dicarlolab/Fiberscope/Software/mex_code/ALP/ALP-4.2/Samples/sequences/SinglePhotographs/valley_LANDSCAPE-FORMAT.jpg

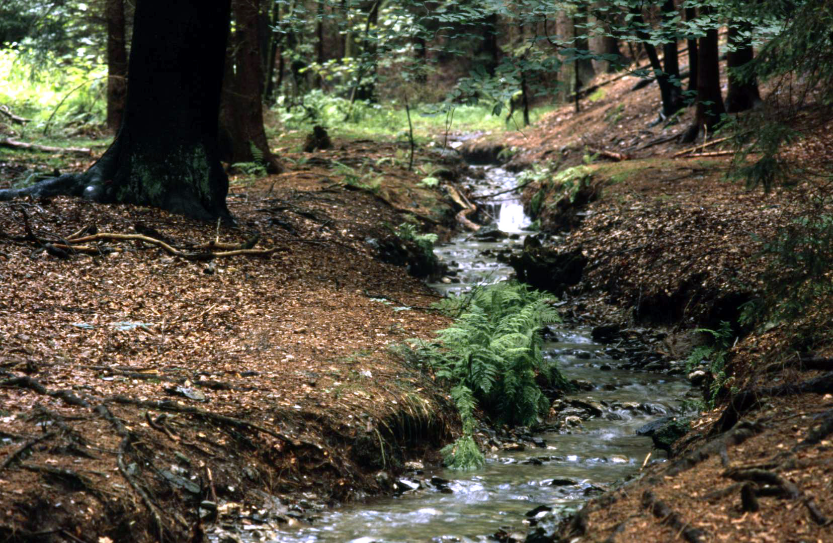
Software/mex_code/ALP/ALP-4.2/Samples/sequences/SinglePhotographs/valley_LANDSCAPE-FORMAT.jpg
