dicarlolab/Fiberscope/Software/mex_code/ALP/ALP-4.2/Samples/sequences/SinglePhotographs/sun-set_PORTRAIT-FORMAT.jpg

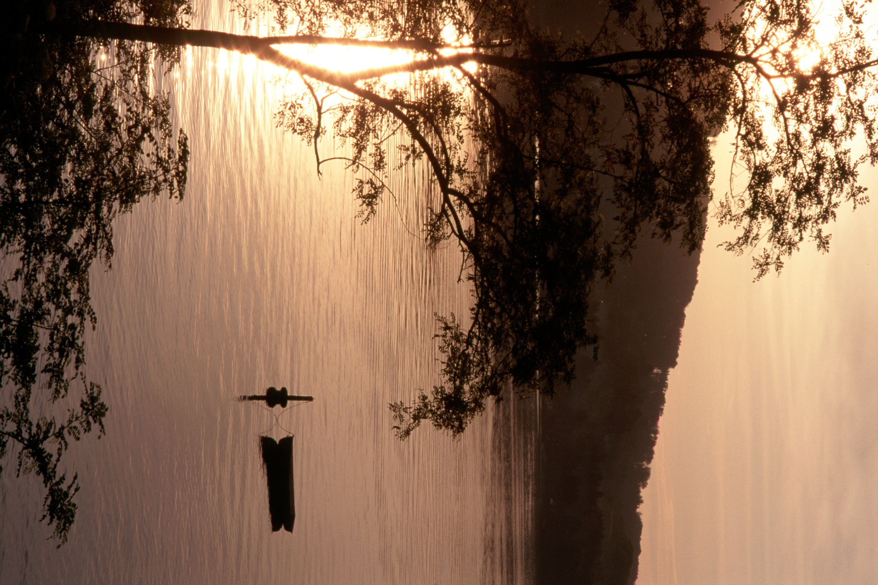
Software/mex_code/ALP/ALP-4.2/Samples/sequences/SinglePhotographs/sun-set_PORTRAIT-FORMAT.jpg
