dicarlolab/Fiberscope/Software/mex_code/ALP/ALP-4.2 v12/Samples/LabVIEW ALP-4.2 high-speed/ALP42_XGA.png

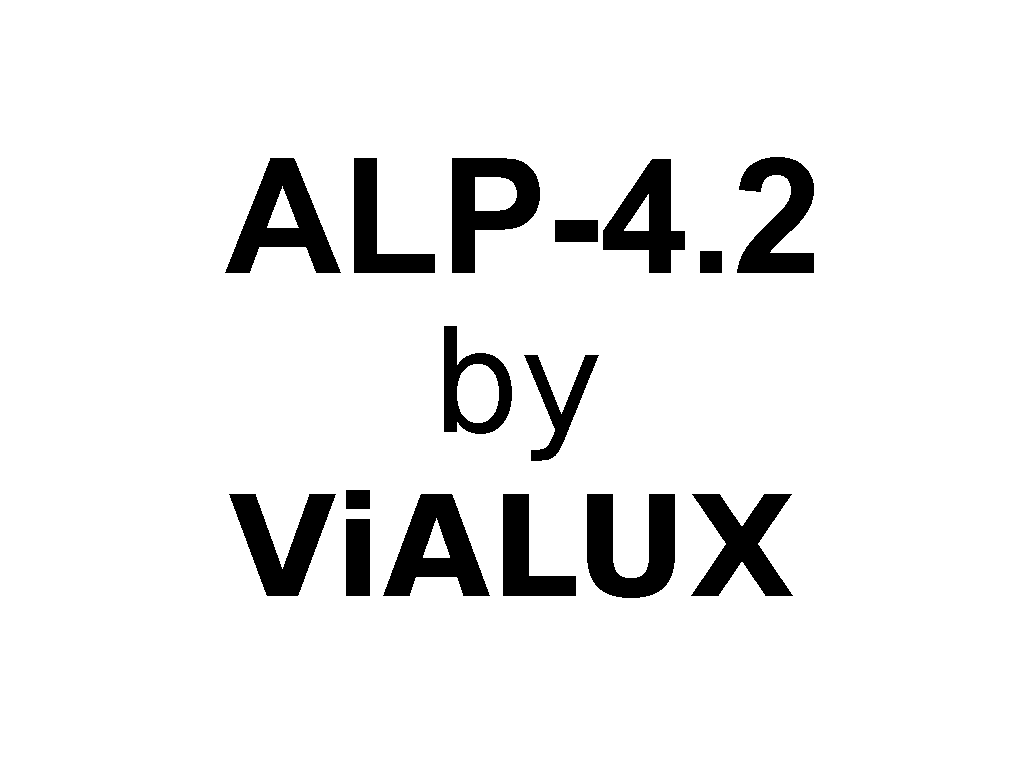
Software/mex_code/ALP/ALP-4.2 v12/Samples/LabVIEW ALP-4.2 high-speed/ALP42_XGA.png
