dicarlolab/Fiberscope/Software/mex_code/ALP/ALP-4.2/Samples/sequences/SequenceTextAndCircle-XGA/ProjectionSequence_Count1024x768_03.png

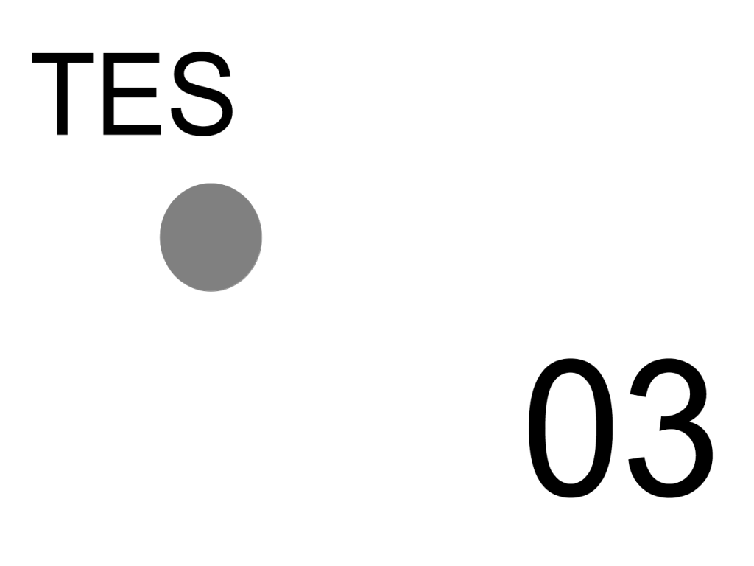
Software/mex_code/ALP/ALP-4.2/Samples/sequences/SequenceTextAndCircle-XGA/ProjectionSequence_Count1024x768_03.png
