dicarlolab/Fiberscope/MechanicalDesign/CP02-Solidworks.sldprt

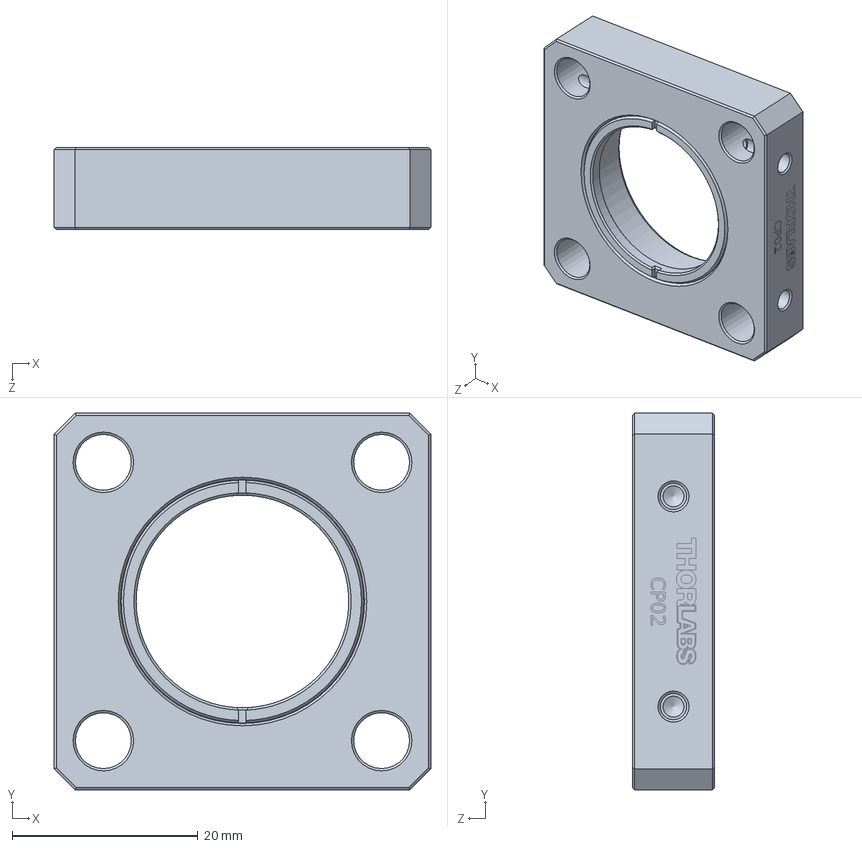
[picture p28: CAD file, 2017-12-06]
MechanicalDesign/CP02-Solidworks.sldprt
40.6 x 40.6 x 8.89 mm
