dicarlolab/Fiberscope/MechanicalDesign/Optic Fiber 105-125um .66NA fiber Neuronexus.SLDPRT

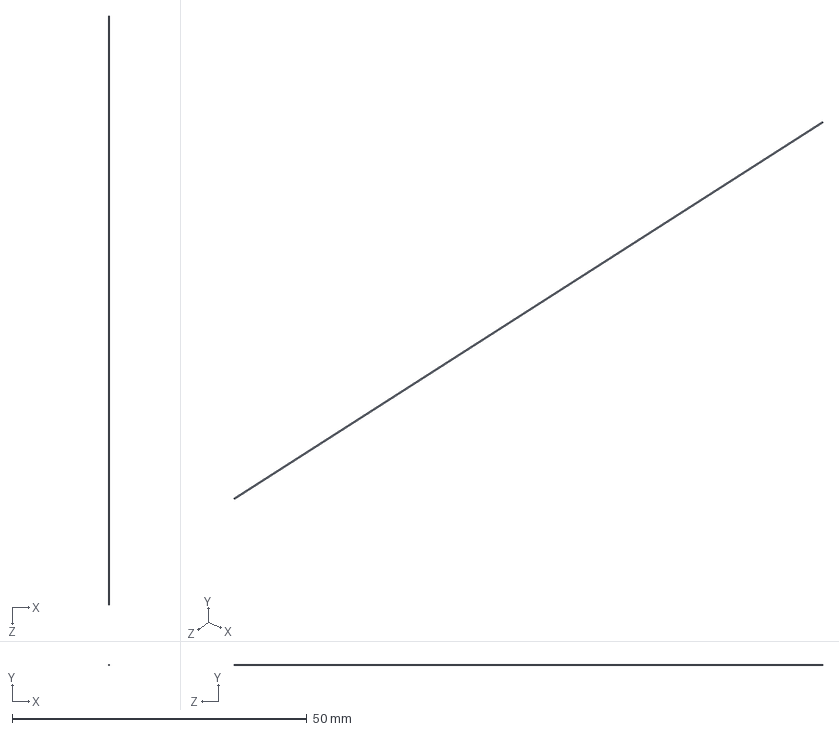
[picture p29: CAD file, 2017-12-06]
MechanicalDesign/Optic Fiber 105-125um .66NA fiber Neuronexus.SLDPRT
0.125 x 0.125 x 100.0 mm
