dicarlolab/Fiberscope/MechanicalDesign/AC127-019-A-ML-Solidworks.sldprt

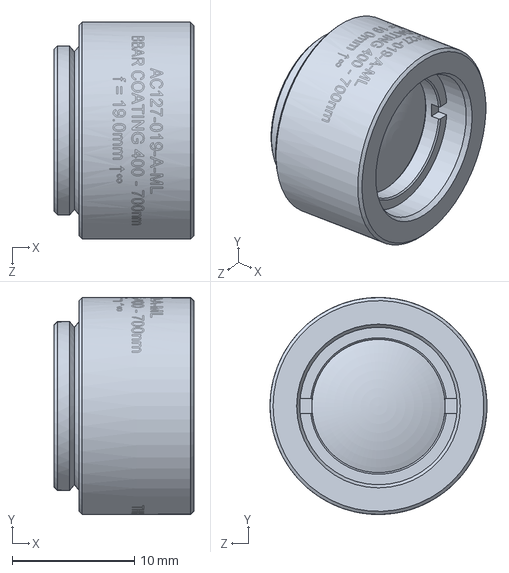
[picture p30: CAD file, 2017-12-06]
MechanicalDesign/AC127-019-A-ML-Solidworks.sldprt
11.4 x 17.8 x 17.8 mm
