dicarlolab/Fiberscope/MechanicalDesign/KM100-E02-Solidworks.sldprt

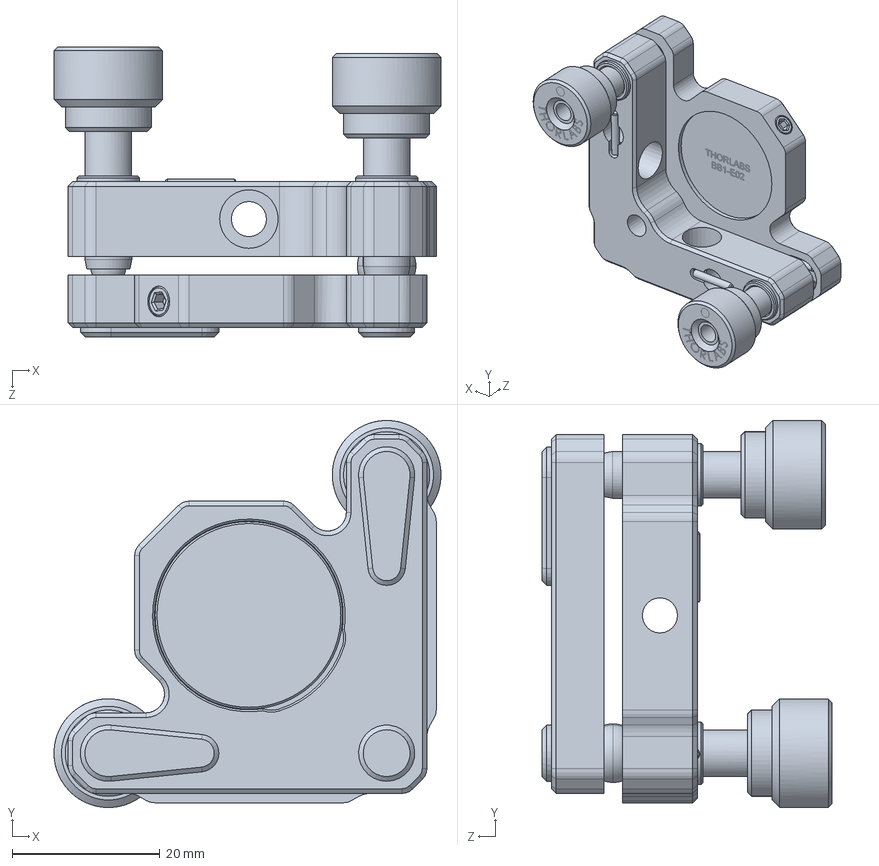
[picture p31: CAD file, 2017-12-06]
MechanicalDesign/KM100-E02-Solidworks.sldprt
52.4 x 52.5 x 39.3 mm
