dicarlolab/Fiberscope/MechanicalDesign/SM05T1-Solidworks.sldprt

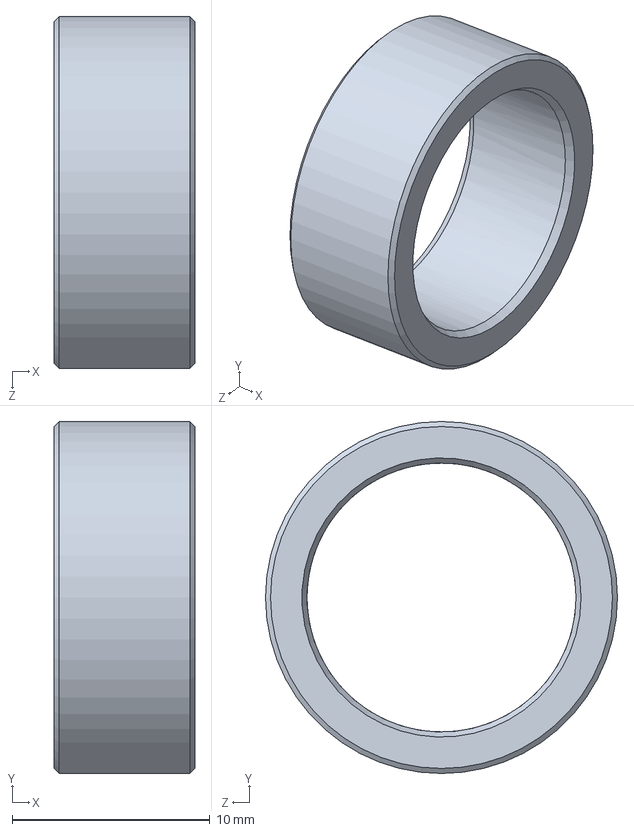
[picture p32: CAD file, 2017-12-06]
MechanicalDesign/SM05T1-Solidworks.sldprt
7.11 x 17.8 x 17.8 mm
