dicarlolab/Fiberscope/MechanicalDesign/SM1L05-Solidworks.sldprt

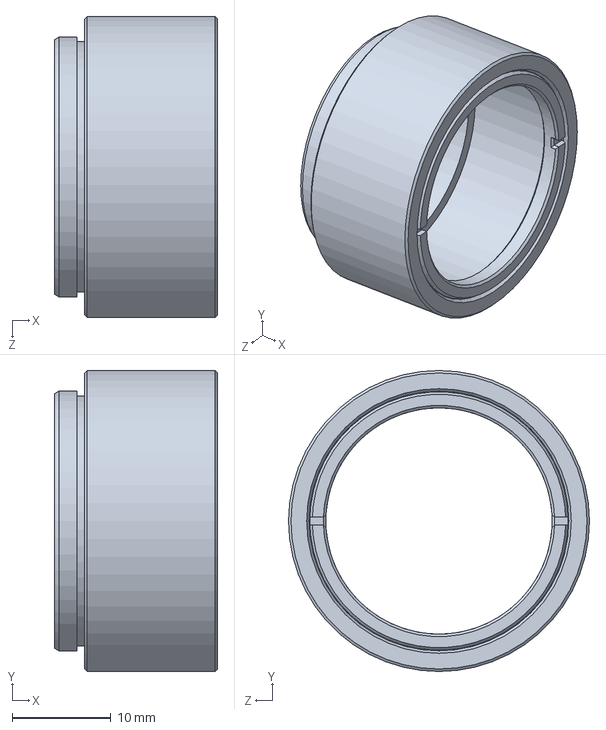
[picture p33: CAD file, 2017-12-06]
MechanicalDesign/SM1L05-Solidworks.sldprt
16.5 x 30.5 x 30.5 mm
