dicarlolab/Fiberscope/MechanicalDesign/SM1A1-Solidworks.sldprt

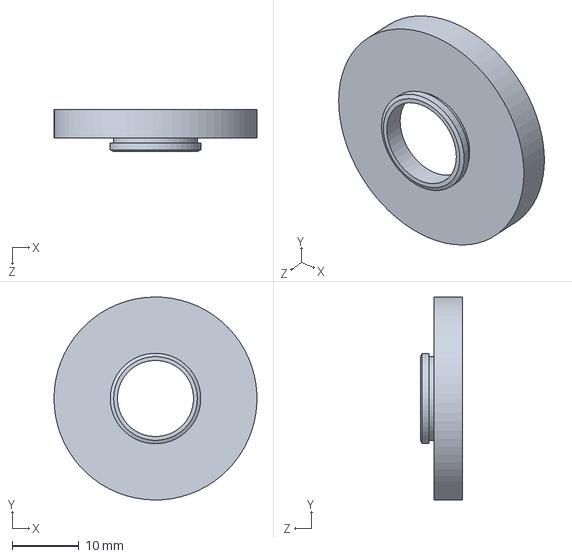
[picture p34: CAD file, 2017-12-06]
MechanicalDesign/SM1A1-Solidworks.sldprt
30.5 x 30.5 x 6.35 mm
