dicarlolab/Fiberscope/MechanicalDesign/Middle_plate_V8Bottom.SLDPRT

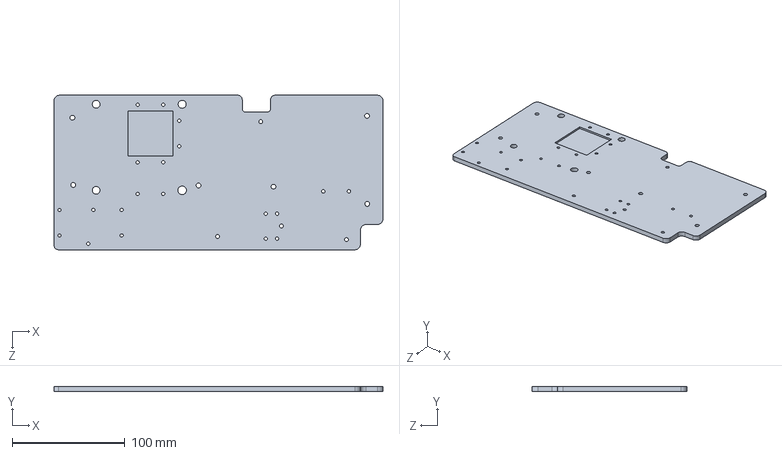
[picture p35: CAD file, 2017-12-06]
MechanicalDesign/Middle_plate_V8Bottom.SLDPRT
291.4 x 4.80 x 137.0 mm
