dicarlolab/Fiberscope/MechanicalDesign/SP05-Solidworks.SLDPRT

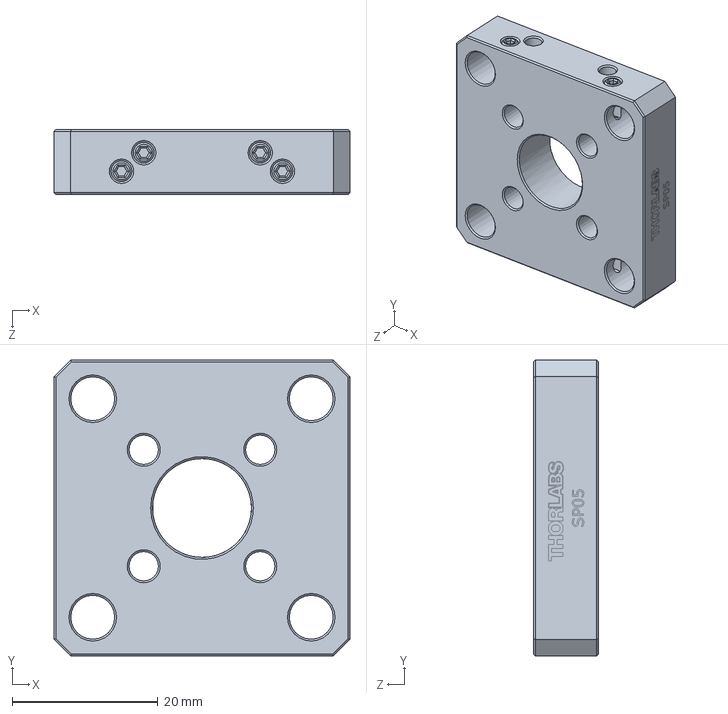
[picture p36: CAD file, 2017-12-06]
MechanicalDesign/SP05-Solidworks.SLDPRT
40.6 x 40.6 x 8.89 mm
