dicarlolab/Fiberscope/MechanicalDesign/CXY1 - 30 mm Cage System, XY Translating Lens Mount for Ø1 Optics .sldprt

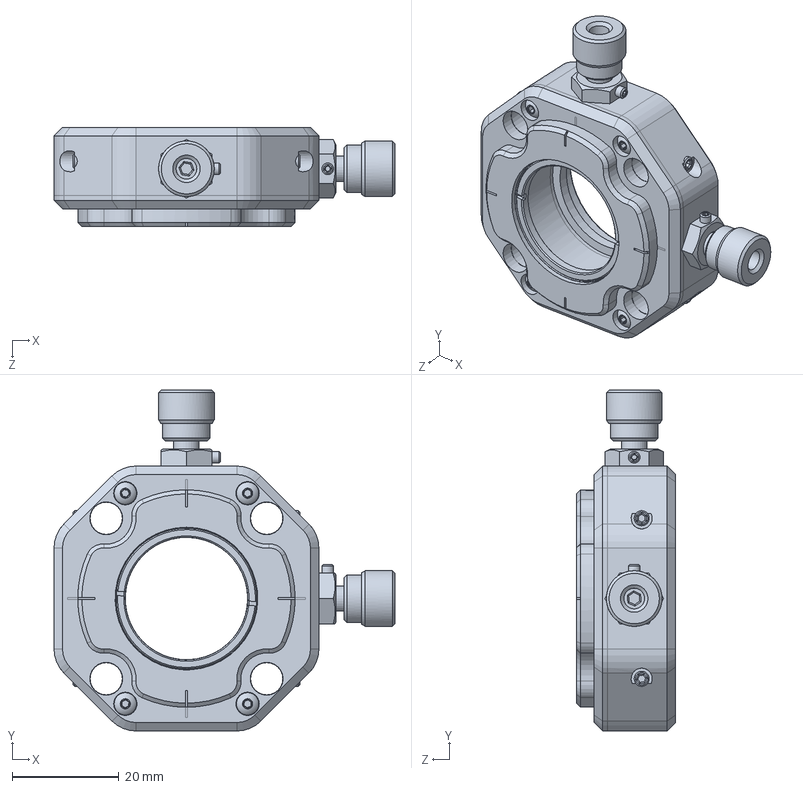
[picture p37: CAD file, 2017-12-06]
MechanicalDesign/CXY1 - 30 mm Cage System, XY Translating Lens Mount for Ø1 Optics .sldprt
63.8 x 63.7 x 18.6 mm
