dicarlolab/Fiberscope/MechanicalDesign/AC254-125-A-ML-Solidworks.sldprt

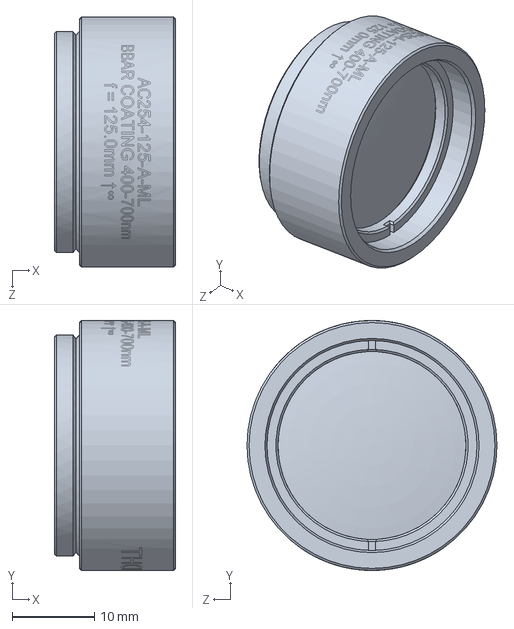
[picture p38: CAD file, 2017-12-06]
MechanicalDesign/AC254-125-A-ML-Solidworks.sldprt
14.8 x 30.5 x 30.5 mm
