dicarlolab/Fiberscope/Software/mex_code/Camera/PTgrey/include/C/FlyCapture2_C.h

//=============================================================================
// Copyright © 2008 Point Grey Research, Inc. All Rights Reserved.
//
// This software is the confidential and proprietary information of Point
// Grey Research, Inc. ("Confidential Information").  You shall not
// disclose such Confidential Information and shall use it only in
// accordance with the terms of the license agreement you entered into
// with PGR.
//
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
#ifndef PGR_FC2_FLYCAPTURE2_C_H
#define PGR_FC2_FLYCAPTURE2_C_H

//=============================================================================
// Global C header file for FlyCapture2. 
//
// This file defines the C API for FlyCapture2
//=============================================================================

#include "FlyCapture2Platform_C.h"
#include "FlyCapture2Defs_C.h"

#ifdef __cplusplus
extern "C"
{
#endif

/**
 * Create a FC2 context for IIDC camaera. 
 * This call must be made before any other calls that use a context
 * will succeed.
 *
 * @param pContext A pointer to the fc2Context to be created.
 *
 * @return A fc2Error indicating the success or failure of the function.
 */
FLYCAPTURE2_C_API fc2Error 
fc2CreateContext(
    fc2Context* pContext );

/**
 * Create a FC2 context for a GigE Vision camera. 
 * This call must be made before any other calls that use a context
 * will succeed.
 *
 * @param pContext A pointer to the fc2Context to be created.
 *
 * @return A fc2Error indicating the success or failure of the function.
 */
FLYCAPTURE2_C_API fc2Error 
fc2CreateGigEContext(
    fc2Context* pContext );

/**
 * Destroy the FC2 context. This must be called when the user is finished
 * with the context in order to prevent memory leaks.
 *
 * @param context The context to be destroyed.
 *
 * @return A fc2Error indicating the success or failure of the function.
 */
FLYCAPTURE2_C_API fc2Error 
fc2DestroyContext(
    fc2Context context );

/** 
 * Fire a bus reset. The actual bus reset is only fired for the 
 * specified 1394 bus, but it will effectively cause a global bus
 * reset for the library.
 *
 * @param context The fc2Context to be used.
 * @param pGuid PGRGuid of the camera or the device to cause bus reset.
 *
 * @return An Error indicating the success or failure of the function.
 */
FLYCAPTURE2_C_API fc2Error 
fc2FireBusReset( 
    fc2Context context,
    fc2PGRGuid* pGuid);

/**
 * Gets the number of cameras attached to the PC.
 *
 * @param context The fc2Context to be used.
 * @param pNumCameras Number of cameras detected.
 *
 * @return A fc2Error indicating the success or failure of the function.
 */
FLYCAPTURE2_C_API fc2Error 
fc2GetNumOfCameras(
    fc2Context context,
    unsigned int* pNumCameras );

/**
 * Query whether a GigE camera is controlable.
 *
 * @param context The fc2Context to be used.
 * @param pGuid Unique PGRGuid for the camera.
 * @param pControlable True indicates camera is controllable
 *
 * @return A fc2Error indicating the success or failure of the function.
 */
FLYCAPTURE2_C_API fc2Error 
fc2IsCameraControlable(
    fc2Context context,
	fc2PGRGuid* pGuid,
    BOOL* pControlable );

/**
 * Gets the PGRGuid for a camera on the PC. It uniquely identifies
 * the camera specified by the index and is used to identify the camera
 * during a fc2Connect() call.
 *
 * @param context The fc2Context to be used.
 * @param index Zero based index of camera.
 * @param pGuid Unique PGRGuid for the camera.
 *
 * @return A fc2Error indicating the success or failure of the function.
 */
FLYCAPTURE2_C_API fc2Error 
fc2GetCameraFromIndex(
    fc2Context context,
    unsigned int index,
    fc2PGRGuid* pGuid );


/**
* Gets the PGRGuid for a camera with the specified IPv4 address.
*
* @param context The fc2Context to be used.
* @param ipAddress IP address to get GUID for.
* @param pGuid Unique PGRGuid for the camera.
*
* @return A fc2Error indicating the success or failure of the function.
*/
FLYCAPTURE2_C_API fc2Error
fc2GetCameraFromIPAddress(
	fc2Context context,
	fc2IPAddress ipAddress,
	fc2PGRGuid* pGuid);

/**
 * Gets the PGRGuid for a camera on the PC. It uniquely identifies
 * the camera specified by the serial number and is used to identify the camera
 * during a fc2Connect() call.
 *
 * @param context The fc2Context to be used.
 * @param serialNumber Serial number of camera.
 * @param pGuid Unique PGRGuid for the camera.
 *
 * @return A fc2Error indicating the success or failure of the function.
 */
FLYCAPTURE2_C_API fc2Error 
fc2GetCameraFromSerialNumber(
    fc2Context context,
    unsigned int serialNumber,
    fc2PGRGuid* pGuid );

/**
 * Gets the serial number of the camera with the specified index.
 *
 * @param context The fc2Context to be used.
 * @param index Zero based index of desired camera.
 * @param pSerialNumber Serial number of camera.
 *
 * @return A fc2Error indicating the success or failure of the function.
 */
FLYCAPTURE2_C_API fc2Error 
fc2GetCameraSerialNumberFromIndex(
    fc2Context context,
    unsigned int index,
    unsigned int* pSerialNumber );

/**
 * Gets the interface type associated with a PGRGuid. This is useful
 * in situations where there is a need to enumerate all cameras
 * for a particular interface.
 *
 * @param context The fc2Context to be used.
 * @param pGuid The PGRGuid to get the interface for.
 * @param pInterfaceType The interface type of the PGRGuid.
 *
 * @return
 */
FLYCAPTURE2_C_API fc2Error 
fc2GetInterfaceTypeFromGuid(
    fc2Context context,
    fc2PGRGuid *pGuid,
    fc2InterfaceType* pInterfaceType );

/**
 * Gets the number of devices. This may include hubs, host controllers
 * and other hardware devices (including cameras).
 *
 * @param context The fc2Context to be used.
 * @param pNumDevices The number of devices found.
 *
 * @return An Error indicating the success or failure of the function.
 */ 
FLYCAPTURE2_C_API fc2Error 
fc2GetNumOfDevices( 
    fc2Context context,
    unsigned int* pNumDevices );

/**
 * Gets the PGRGuid for a device. It uniquely identifies the device
 * specified by the index.
 *
 * @param context The fc2Context to be used.
 * @param index Zero based index of device.
 * @param pGuid Unique PGRGuid for the device.
 *
 * @see fc2GetNumOfDevices()
 *
 * @return An Error indicating the success or failure of the function.
 */ 
FLYCAPTURE2_C_API fc2Error 
fc2GetDeviceFromIndex( 
    fc2Context context,
    unsigned int index, 
    fc2PGRGuid*     pGuid );

/**
 * Register a callback function that will be called when the
 * specified callback event occurs.
 *
 * @param context The fc2Context to be used.
 * @param enumCallback Pointer to function that will receive the callback.
 * @param callbackType Type of callback to register for.
 * @param pParameter Callback parameter to be passed to callback.
 * @param pCallbackHandle Unique callback handle used for unregistering 
 *                        callback.
 *
 * @return A fc2Error indicating the success or failure of the function.
 */
FLYCAPTURE2_C_API fc2Error 
fc2RegisterCallback(
    fc2Context context,
    fc2BusEventCallback enumCallback,
    fc2BusCallbackType callbackType,
    void* pParameter,
    fc2CallbackHandle* pCallbackHandle );

/**
 * Unregister a callback function.
 *
 * @param context The fc2Context to be used.
 * @param callbackHandle Unique callback handle.
 *
 * @return A fc2Error indicating the success or failure of the function.
 */
FLYCAPTURE2_C_API fc2Error 
fc2UnregisterCallback(
    fc2Context context,
    fc2CallbackHandle callbackHandle );

/**
 * Force a rescan of the buses. This does not trigger a bus reset.
 * However, any current connections to a Camera object will be
 * invalidated.
 *
 * @return An Error indicating the success or failure of the function.
 */ 
FLYCAPTURE2_C_API fc2Error 
fc2RescanBus( fc2Context context);

/**
 * Force the camera with the specific MAC address to the specified
 * IP address, subnet mask and default gateway. This is useful in
 * situations where a GigE Vision camera is using Persistent IP and the
 * application's subnet is different from the device subnet.
 *
 * @param context The fc2Context to be used.
 * @param macAddress MAC address of the camera.
 * @param ipAddress IP address to set on the camera.
 * @param subnetMask Subnet mask to set on the camera.
 * @param defaultGateway Default gateway to set on the camera.
 *
 * @return An Error indicating the success or failure of the function.
 */
FLYCAPTURE2_C_API fc2Error 
fc2ForceIPAddressToCamera( 
    fc2Context context,
    fc2MACAddress macAddress,
    fc2IPAddress ipAddress,
    fc2IPAddress subnetMask,
    fc2IPAddress defaultGateway );

/**
* Force all cameras on the network to be assigned sequential IP addresses
* on the same subnet as the netowrk adapters that they are connected to. 
* This is useful in situations where a GigE Vision cameras are using 
* Persistent IP addresses and the application's subnet is different from 
* the devices.
*
* @return An Error indicating the success or failure of the function.
*/
FLYCAPTURE2_C_API fc2Error
fc2ForceAllIPAddressesAutomatically();

/**
* Force a cameras on the network to be assigned sequential IP addresses
* on the same subnet as the netowrk adapters that it is connected to. 
* This is useful in situations where a GigE Vision cameras is using 
* Persistent IP addresses and the application's subnet is different from 
* the device.
*
* @return An Error indicating the success or failure of the function.
*/
FLYCAPTURE2_C_API fc2Error
fc2ForceIPAddressAutomatically(unsigned int serialNumber);

/**
 * Discover all cameras connected to the network even if they reside
 * on a different subnet. This is useful in situations where a GigE
 * camera is using Persistent IP and the application's subnet is
 * different from the device subnet. After discovering the camera,  
 * it is easy to use ForceIPAddressToCamera() to set a different IP 
 * configuration.
 *
 * @param context The fc2Context to be used.
 * @param gigECameras Pointer to an array of CameraInfo structures.
 * @param arraySize Size of the array. Number of discovered cameras
 *                  is returned in the same value.
 *
 * @return An Error indicating the success or failure of the function.
 *         If the error is PGRERROR_BUFFER_TOO_SMALL then arraySize will
 *         contain the minimum size needed for gigECameras array.
 */
FLYCAPTURE2_C_API fc2Error 
fc2DiscoverGigECameras( 
    fc2Context context,
    fc2CameraInfo* gigECameras,
    unsigned int* arraySize  );

/**
 * Write to the specified register on the camera.
 *
 * @param context The fc2Context to be used.
 * @param address DCAM address to be written to.
 * @param value The value to be written.
 *
 * @return A fc2Error indicating the success or failure of the function.
 */
FLYCAPTURE2_C_API fc2Error 
fc2WriteRegister(
    fc2Context context,
    unsigned int address,
    unsigned int value);

/**
 * Write to the specified register on the camera with broadcast.
 *
 * @param context The fc2Context to be used.
 * @param address DCAM address to be written to.
 * @param value The value to be written.
 *
 * @return A fc2Error indicating the success or failure of the function.
 */
FLYCAPTURE2_C_API fc2Error 
fc2WriteRegisterBroadcast(
    fc2Context context,
    unsigned int address,
    unsigned int value);

/**
 * Read the specified register from the camera.
 *
 * @param context The fc2Context to be used.
 * @param address DCAM address to be read from.
 * @param pValue The value that is read.
 *
 * @return A fc2Error indicating the success or failure of the function.
 */
FLYCAPTURE2_C_API fc2Error 
fc2ReadRegister(
    fc2Context context,
    unsigned int address,
    unsigned int* pValue );

/**
 * Write to the specified register block on the camera.
 *
 * @param context The fc2Context to be used.
 * @param addressHigh Top 16 bits of the 48 bit absolute address to write to.
 * @param addressLow Bottom 32 bits of the 48 bits absolute address to write to.              
 * @param pBuffer Array containing data to be written.
 * @param length Size of array, in quadlets.
 *
 * @return A fc2Error indicating the success or failure of the function.
 */
FLYCAPTURE2_C_API fc2Error 
fc2WriteRegisterBlock(
    fc2Context context,
    unsigned short addressHigh,
    unsigned int addressLow,
    const unsigned int* pBuffer,
    unsigned int length );

/**
 * Write to the specified register block on the camera.
 *
 * @param context The fc2Context to be used.
 * @param addressHigh Top 16 bits of the 48 bit absolute address to read from.
 * @param addressLow Bottom 32 bits of the 48 bits absolute address to read from.                
 * @param pBuffer Array to store read data.
 * @param length Size of array, in quadlets.
 *
 * @return A fc2Error indicating the success or failure of the function.
 */
FLYCAPTURE2_C_API fc2Error 
fc2ReadRegisterBlock(
    fc2Context context,
    unsigned short addressHigh,
    unsigned int addressLow,
    unsigned int* pBuffer,
    unsigned int length );     

/**
 * Connects the camera object to the camera specified by the GUID.
 *
 * @param context The fc2Context to be used.
 * @param guid The unique identifier for a specific camera on the PC.
 *
 * @return A fc2Error indicating the success or failure of the function.
 */
FLYCAPTURE2_C_API fc2Error 
fc2Connect( 
    fc2Context context,
    fc2PGRGuid* guid );

/**
 * Disconnects the fc2Context from the camera.
 *
 * @param context The fc2Context to be used.
 *
 * @return A fc2Error indicating the success or failure of the function.
 */
FLYCAPTURE2_C_API fc2Error 
fc2Disconnect( 
    fc2Context context );

/**
 * Sets the callback data to be used on completion of image transfer.
 * To clear the current stored callback data, pass in NULL for both
 * callback arguments.
 *
 * @param context The fc2Context to be used.
 * @param pCallbackFn A function to be called when a new image is received.
 * @param pCallbackData A pointer to data that can be passed to the
 *                      callback function.
 *
 * @return A fc2Error indicating the success or failure of the function.
 */
FLYCAPTURE2_C_API fc2Error
fc2SetCallback(
    fc2Context context,
    fc2ImageEventCallback pCallbackFn,
    void* pCallbackData);

/**
 * Starts isochronous image capture. It will use either the current
 * video mode or the most recently set video mode of the camera.
 *
 * @param context The fc2Context to be used.
 *
 * @return A fc2Error indicating the success or failure of the function.
 */
FLYCAPTURE2_C_API fc2Error 
fc2StartCapture( 
    fc2Context context );

/**
 * Starts isochronous image capture. It will use either the current
 * video mode or the most recently set video mode of the camera. The callback
 * function is called when a new image is received from the camera.
 *
 * @param context The fc2Context to be used.
 * @param pCallbackFn A function to be called when a new image is received.        
 * @param pCallbackData A pointer to data that can be passed to the
 *                      callback function. A NULL pointer is acceptable.
 *
 * @return A fc2Error indicating the success or failure of the function.
 */
FLYCAPTURE2_C_API fc2Error 
fc2StartCaptureCallback(
    fc2Context context,
    fc2ImageEventCallback pCallbackFn,
    void* pCallbackData);

/**
 * Starts synchronized isochronous image capture on multiple cameras.
 *
 * @param numCameras Number of fc2Contexts in the ppCameras array.
 * @param pContexts Array of fc2Contexts.
 *
 * @return A fc2Error indicating the success or failure of the function.
 */
FLYCAPTURE2_C_API fc2Error 
fc2StartSyncCapture( 
    unsigned int numCameras, 
    fc2Context *pContexts );

/**
 * Starts synchronized isochronous image capture on multiple cameras.
 *
 * @param numCameras Number of fc2Contexts in the ppCameras array.
 * @param pContexts Array of fc2Contexts.
 * @param pCallbackFns Array of callback functions for each camera.
 * @param pCallbackDataArray Array of callback data pointers. 
 *
 * @return A fc2Error indicating the success or failure of the function.
 */
FLYCAPTURE2_C_API fc2Error 
fc2StartSyncCaptureCallback( 
    unsigned int numCameras, 
    fc2Context *pContexts,
    fc2ImageEventCallback* pCallbackFns,
    void** pCallbackDataArray);

/**
 * Retrieves the the next image object containing the next image.
 *
 * @param context The fc2Context to be used.
 * @param pImage Pointer to fc2Image to store image data.
 *
 * @return A fc2Error indicating the success or failure of the function.
 */
FLYCAPTURE2_C_API fc2Error 
fc2RetrieveBuffer( 
    fc2Context context,
    fc2Image* pImage );

/**
 * Stops isochronous image transfer and cleans up all associated
 * resources.
 *
 * @param context The fc2Context to be used.
 *
 * @return A fc2Error indicating the success or failure of the function.
 */
FLYCAPTURE2_C_API fc2Error 
fc2StopCapture( 
    fc2Context context );

/**
 * Specify user allocated buffers to use as image data buffers.
 *
 * @param context The fc2Context to be used.
 * @param ppMemBuffers Pointer to memory buffers to be written to. The
 *                     size of the data should be equal to 
 *                     (size * numBuffers) or larger.
 * @param size The size of each buffer (in bytes).
 * @param nNumBuffers Number of buffers in the array.
 *
 * @return A fc2Error indicating the success or failure of the function.
 */
FLYCAPTURE2_C_API fc2Error 
fc2SetUserBuffers(
    fc2Context context,
    unsigned char* const ppMemBuffers,
    int size,
    int nNumBuffers );

/**
 * Get the configuration associated with the camera.
 *
 * @param context The fc2Context to be used.
 * @param config Pointer to the configuration structure to be filled.
 *
 * @return A fc2Error indicating the success or failure of the function.
 */
FLYCAPTURE2_C_API fc2Error 
fc2GetConfiguration( 
    fc2Context context,
    fc2Config* config );

/**
 * Set the configuration associated with the camera.
 *
 * @param context The fc2Context to be used.
 * @param config Pointer to the configuration structure to be used.
 *
 * @return A fc2Error indicating the success or failure of the function.
 */
FLYCAPTURE2_C_API fc2Error 
fc2SetConfiguration( 
    fc2Context context,
    fc2Config* config );

/**
 * Retrieves information from the camera such as serial number, model
 * name and other camera information.
 *
 * @param context The fc2Context to be used.
 * @param pCameraInfo Pointer to the camera information structure
 *                    to be filled.
 *
 * @return A fc2Error indicating the success or failure of the function.
 */
FLYCAPTURE2_C_API fc2Error 
fc2GetCameraInfo( 
    fc2Context context,
    fc2CameraInfo* pCameraInfo );

/**
 * Retrieves information about the specified camera property. The 
 * property type must be specified in the fc2PropertyInfo structure 
 * passed into the function in order for the function to succeed.
 *
 * @param context The fc2Context to be used.
 * @param propInfo Pointer to the PropertyInfo structure to be filled.
 *
 * @return A fc2Error indicating the success or failure of the function.
 */
FLYCAPTURE2_C_API fc2Error 
fc2GetPropertyInfo( 
    fc2Context context,
    fc2PropertyInfo* propInfo );

/**
 * Reads the settings for the specified property from the camera. The 
 * property type must be specified in the fc2Property structure passed
 * into the function in order for the function to succeed. If auto
 * is on, the integer and abs values returned may not be consistent
 * with each other.
 *
 * @param context The fc2Context to be used.
 * @param prop Pointer to the Property structure to be filled.
 *
 * @return A fc2Error indicating the success or failure of the function.
 */
FLYCAPTURE2_C_API fc2Error 
fc2GetProperty( 
    fc2Context context,
    fc2Property* prop );

/**
 * Writes the settings for the specified property to the camera. The 
 * property type must be specified in the Property structure passed
 * into the function in order for the function to succeed.
 * The absControl flag controls whether the absolute or integer value
 * is written to the camera.
 *
 * @param context The fc2Context to be used.
 * @param prop Pointer to the Property structure to be used.
 *
 * @return A fc2Error indicating the success or failure of the function.
 */
FLYCAPTURE2_C_API fc2Error 
fc2SetProperty( 
    fc2Context context,
    fc2Property* prop );

/**
 * Writes the settings for the specified property to the camera. The 
 * property type must be specified in the Property structure passed
 * into the function in order for the function to succeed.
 * The absControl flag controls whether the absolute or integer value
 * is written to the camera.
 *
 * @param context The fc2Context to be used.
 * @param prop Pointer to the Property structure to be used.
 *
 * @return A fc2Error indicating the success or failure of the function.
 */
FLYCAPTURE2_C_API fc2Error 
fc2SetPropertyBroadcast( 
    fc2Context context,
    fc2Property* prop );

/**
 * Get the GPIO pin direction for the specified pin. This is not a
 * required call when using the trigger or strobe functions as
 * the pin direction is set automatically internally.
 *
 * @param context The fc2Context to be used.
 * @param pin Pin to get the direction for.
 * @param pDirection Direction of the pin. 0 for input, 1 for output.
 *
 * @return A fc2Error indicating the success or failure of the function.
 */
FLYCAPTURE2_C_API fc2Error 
fc2GetGPIOPinDirection( 
    fc2Context context,
    unsigned int pin, 
    unsigned int* pDirection );

/**
 * Set the GPIO pin direction for the specified pin. This is useful if
 * there is a need to set the pin into an input pin (i.e. to read the
 * voltage) off the pin without setting it as a trigger source. This 
 * is not a required call when using the trigger or strobe functions as
 * the pin direction is set automatically internally.
 *
 * @param context The fc2Context to be used.
 * @param pin Pin to get the direction for.
 * @param direction Direction of the pin. 0 for input, 1 for output.
 *
 * @return A fc2Error indicating the success or failure of the function.
 */
FLYCAPTURE2_C_API fc2Error 
fc2SetGPIOPinDirection( 
    fc2Context context,
    unsigned int pin, 
    unsigned int direction);

/**
 * Set the GPIO pin direction for the specified pin. This is useful if
 * there is a need to set the pin into an input pin (i.e. to read the
 * voltage) off the pin without setting it as a trigger source. This 
 * is not a required call when using the trigger or strobe functions as
 * the pin direction is set automatically internally.
 *
 * @param context The fc2Context to be used.
 * @param pin Pin to get the direction for.
 * @param direction Direction of the pin. 0 for input, 1 for output.
 *
 * @return A fc2Error indicating the success or failure of the function.
 */
FLYCAPTURE2_C_API fc2Error 
fc2SetGPIOPinDirectionBroadcast( 
    fc2Context context,
    unsigned int pin, 
    unsigned int direction);

/**
 * Retrieve trigger information from the camera.
 *
 * @param context The fc2Context to be used.
 * @param triggerModeInfo Structure to receive trigger information.
 *
 * @return A fc2Error indicating the success or failure of the function.
 */
FLYCAPTURE2_C_API fc2Error 
fc2GetTriggerModeInfo( 
    fc2Context context,
    fc2TriggerModeInfo* triggerModeInfo );

/**
 * Retrieve current trigger settings from the camera.
 *
 * @param context The fc2Context to be used.
 * @param triggerMode Structure to receive trigger mode settings.
 *
 * @return A fc2Error indicating the success or failure of the function.
 */
FLYCAPTURE2_C_API fc2Error 
fc2GetTriggerMode( 
    fc2Context context,
    fc2TriggerMode* triggerMode );

/**
 * Set the specified trigger settings to the camera.
 *
 * @param context The fc2Context to be used.
 * @param triggerMode Structure providing trigger mode settings.
 *
 * @return A fc2Error indicating the success or failure of the function.
 */
FLYCAPTURE2_C_API fc2Error 
fc2SetTriggerMode( 
    fc2Context context,
    fc2TriggerMode* triggerMode );

/**
 * Set the specified trigger settings to the camera.
 *
 * @param context The fc2Context to be used.
 * @param triggerMode Structure providing trigger mode settings.
 *
 * @return A fc2Error indicating the success or failure of the function.
 */
FLYCAPTURE2_C_API fc2Error 
fc2SetTriggerModeBroadcast( 
    fc2Context context,
    fc2TriggerMode* triggerMode );

/**
 * 
 *
 * @param context The fc2Context to be used.
 *
 * @return A fc2Error indicating the success or failure of the function.
 */
FLYCAPTURE2_C_API fc2Error 
fc2FireSoftwareTrigger(
    fc2Context context );

/**
 * Fire the software trigger according to the DCAM specifications.
 *
 * @param context The fc2Context to be used.
 *
 * @return A fc2Error indicating the success or failure of the function.
 */
FLYCAPTURE2_C_API fc2Error 
fc2FireSoftwareTriggerBroadcast(
    fc2Context context );

/**
 * Retrieve trigger delay information from the camera.
 *
 * @param context The fc2Context to be used.
 * @param triggerDelayInfo Structure to receive trigger delay information.
 *
 * @return A fc2Error indicating the success or failure of the function.
 */
FLYCAPTURE2_C_API fc2Error 
fc2GetTriggerDelayInfo( 
    fc2Context context,
    fc2TriggerDelayInfo* triggerDelayInfo );

/**
 * Retrieve current trigger delay settings from the camera.
 *
 * @param context The fc2Context to be used.
 * @param triggerDelay Structure to receive trigger delay settings.
 *
 * @return A fc2Error indicating the success or failure of the function.
 */
FLYCAPTURE2_C_API fc2Error 
fc2GetTriggerDelay( 
    fc2Context context,
    fc2TriggerDelay* triggerDelay );

/**
 * Set the specified trigger delay settings to the camera.
 *
 * @param context The fc2Context to be used.
 * @param triggerDelay Structure providing trigger delay settings.
 *
 * @return A fc2Error indicating the success or failure of the function.
 */
FLYCAPTURE2_C_API fc2Error 
fc2SetTriggerDelay( 
    fc2Context context,
    fc2TriggerDelay* triggerDelay );

/**
 * Set the specified trigger delay settings to the camera.
 *
 * @param context The fc2Context to be used.
 * @param triggerDelay Structure providing trigger delay settings.
 *
 * @return A fc2Error indicating the success or failure of the function.
 */
FLYCAPTURE2_C_API fc2Error 
fc2SetTriggerDelayBroadcast( 
    fc2Context context,
    fc2TriggerDelay* triggerDelay );

/**
 * Retrieve strobe information from the camera.
 *
 * @param context The fc2Context to be used.
 * @param strobeInfo Structure to receive strobe information.
 *
 * @return A fc2Error indicating the success or failure of the function.
 */
FLYCAPTURE2_C_API fc2Error 
fc2GetStrobeInfo( 
    fc2Context context,
    fc2StrobeInfo* strobeInfo );

/**
 * Retrieve current strobe settings from the camera. The strobe pin
 * must be specified in the structure before being passed in to
 * the function.
 *
 * @param context The fc2Context to be used.
 * @param strobeControl Structure to receive strobe settings.
 *
 * @return A fc2Error indicating the success or failure of the function.
 */
FLYCAPTURE2_C_API fc2Error 
fc2GetStrobe( 
    fc2Context context,
    fc2StrobeControl* strobeControl );

/**
 * Set current strobe settings to the camera. The strobe pin
 * must be specified in the structure before being passed in to
 * the function.
 *
 * @param context The fc2Context to be used.
 * @param strobeControl Structure providing strobe settings.
 *
 * @return A fc2Error indicating the success or failure of the function.
 */
FLYCAPTURE2_C_API fc2Error 
fc2SetStrobe( 
    fc2Context context,
    fc2StrobeControl* strobeControl );

/**
 * Set current strobe settings to the camera. The strobe pin
 * must be specified in the structure before being passed in to
 * the function.
 *
 * @param context The fc2Context to be used.
 * @param strobeControl Structure providing strobe settings.
 *
 * @return A fc2Error indicating the success or failure of the function.
 */
FLYCAPTURE2_C_API fc2Error 
fc2SetStrobeBroadcast( 
    fc2Context context,
    fc2StrobeControl* strobeControl );

/**
 * Query the camera to determine if the specified video mode and 
 * frame rate is supported.
 *
 * @param context The fc2Context to be used.
 * @param videoMode Video mode to check.
 * @param frameRate Frame rate to check.
 * @param pSupported Whether the video mode and frame rate is supported.
 *
 * @return A fc2Error indicating the success or failure of the function.
 */
FLYCAPTURE2_C_API fc2Error 
fc2GetVideoModeAndFrameRateInfo(
    fc2Context context,
    fc2VideoMode videoMode,
    fc2FrameRate frameRate,
    BOOL* pSupported);

/**
 * Get the current video mode and frame rate from the camera. If
 * the camera is in Format7, the video mode will be VIDEOMODE_FORMAT7
 * and the frame rate will be FRAMERATE_FORMAT7.
 *
 * @param context The fc2Context to be used.
 * @param videoMode Current video mode.
 * @param frameRate Current frame rate.
 *
 * @return A fc2Error indicating the success or failure of the function.
 */
FLYCAPTURE2_C_API fc2Error 
fc2GetVideoModeAndFrameRate(
    fc2Context context,
    fc2VideoMode* videoMode,
    fc2FrameRate* frameRate );

/**
 * Set the specified video mode and frame rate to the camera. It is
 * not possible to set the camera to VIDEOMODE_FORMAT7 or 
 * FRAMERATE_FORMAT7. Use the Format7 functions to set the camera
 * into Format7.
 *
 * @param context The fc2Context to be used.
 * @param videoMode Video mode to set to camera.
 * @param frameRate Frame rate to set to camera.
 *
 * @return A fc2Error indicating the success or failure of the function.
 */
FLYCAPTURE2_C_API fc2Error 
fc2SetVideoModeAndFrameRate(
    fc2Context context,
    fc2VideoMode videoMode,
    fc2FrameRate frameRate );

/**
 * Retrieve the availability of Format7 custom image mode and the
 * camera capabilities for the specified Format7 mode. The mode must
 * be specified in the Format7Info structure in order for the
 * function to succeed.
 *
 * @param context The fc2Context to be used.
 * @param info Structure to be filled with the capabilities of the specified
 *             mode and the current state in the specified mode.
 * @param pSupported Whether the specified mode is supported.
 *
 * @return A fc2Error indicating the success or failure of the function.
 */
FLYCAPTURE2_C_API fc2Error 
fc2GetFormat7Info( 
    fc2Context context,
    fc2Format7Info* info,
    BOOL* pSupported );

/**
 * Validates Format7ImageSettings structure and returns valid packet
 * size information if the image settings are valid. The current
 * image settings are cached while validation is taking place. The
 * cached settings are restored when validation is complete.
 *
 * @param context The fc2Context to be used.
 * @param imageSettings Structure containing the image settings.
 * @param settingsAreValid Whether the settings are valid.
 * @param packetInfo Packet size information that can be used to
 *                   determine a valid packet size.
 *
 * @return A fc2Error indicating the success or failure of the function.
 */
FLYCAPTURE2_C_API fc2Error 
fc2ValidateFormat7Settings( 
    fc2Context context,
    fc2Format7ImageSettings* imageSettings,
    BOOL* settingsAreValid,
    fc2Format7PacketInfo* packetInfo );

/**
 * Get the current Format7 configuration from the camera. This call
 * will only succeed if the camera is already in Format7.
 *
 * @param context The fc2Context to be used.
 * @param imageSettings Current image settings.
 * @param packetSize Current packet size.
 * @param percentage Current packet size as a percentage.
 *
 * @return A fc2Error indicating the success or failure of the function.
 */
FLYCAPTURE2_C_API fc2Error 
fc2GetFormat7Configuration( 
    fc2Context context,
    fc2Format7ImageSettings* imageSettings,
    unsigned int* packetSize,
    float* percentage );

/**
 * Set the current Format7 configuration to the camera.
 *
 * @param context The fc2Context to be used.
 * @param imageSettings Image settings to be written to the camera.
 * @param packetSize Packet size to be written to the camera.
 *
 * @return A fc2Error indicating the success or failure of the function.
 */
FLYCAPTURE2_C_API fc2Error 
fc2SetFormat7ConfigurationPacket( 
    fc2Context context,
    fc2Format7ImageSettings* imageSettings,
    unsigned int packetSize );

/**
* Set the current Format7 configuration to the camera.
*
* @param context The fc2Context to be used.
* @param imageSettings Image settings to be written to the camera.
* @param percentSpeed Packet size as a percentage to be written to the camera.
*
* @return A fc2Error indicating the success or failure of the function.
*/
FLYCAPTURE2_C_API fc2Error 
fc2SetFormat7Configuration(
    fc2Context context,
    fc2Format7ImageSettings* imageSettings,
    float percentSpeed );
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
